L10N37/Super-1-RGB-bypass-for-1-chip-SNES-SFC-and-early-Nintendo-64/Photos/20220622_120046.jpg

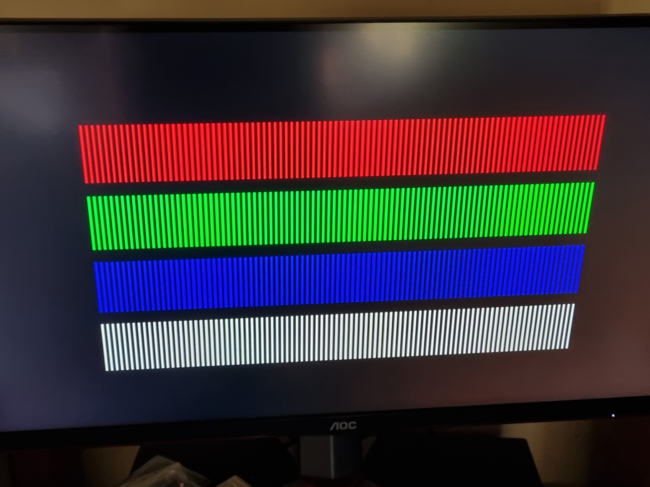
Photos/20220622_120046.jpg
