L10N37/Super-1-RGB-bypass-for-1-chip-SNES-SFC-and-early-Nintendo-64/Early Nintendo 64/P_20221030_150629.jpg

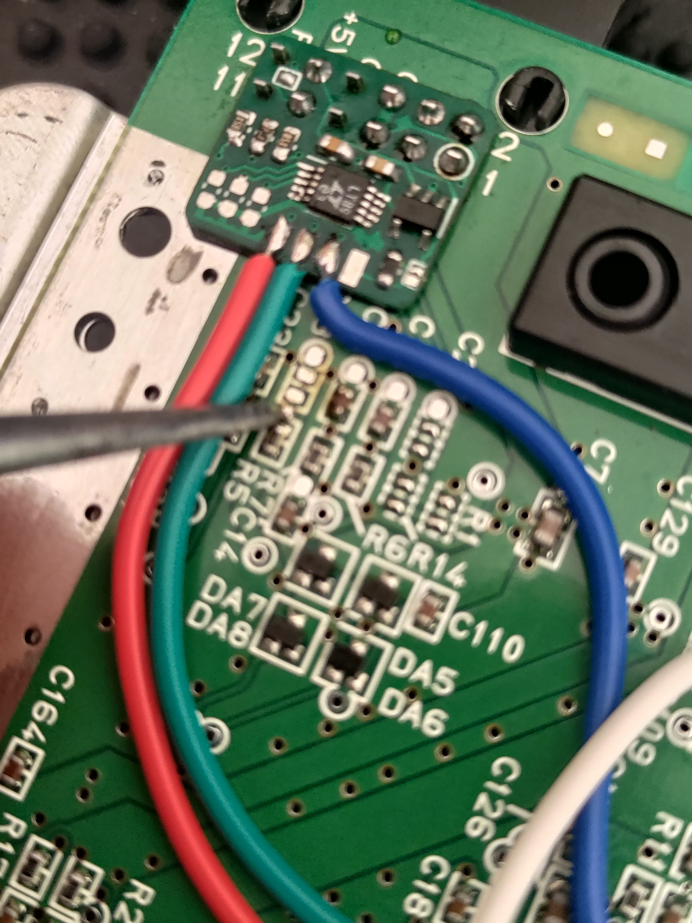
Early Nintendo 64/P_20221030_150629.jpg
